nodep/7g-wireless/src/common/rf_addr.c

#include <stdint.h>

#include "tgtdefs.h"
#include "rf_protocol.h"

const uint8_t DongleAddr1[NRF_ADDR_SIZE] = {0x36, 0xC4, 0x31, 0x40, 0x03};
const uint8_t DongleAddr2[NRF_ADDR_SIZE] = {0x63, 0x4C, 0x30, 0x10, 0x01};
